JakePeak/BLE-Motion-Tracker/Windows_Application/BLE_Computer_Interaction/BLE_Computer_Interaction/resource.h

//{{NO_DEPENDENCIES}}
// Microsoft Visual C++ generated include file.
// Used by BLE_Computer_Interaction.rc
//
#define IDC_MYICON                      2
#define IDD_BLECOMPUTERINTERACTION_DIALOG 102
#define IDS_APP_TITLE                   103
#define IDD_ABOUTBOX                    103
#define IDM_ABOUT                       104
#define IDM_EXIT                        105
#define IDI_BLECOMPUTERINTERACTION      107
#define IDI_SMALL                       108
#define IDC_BLECOMPUTERINTERACTION      109
#define IDR_MAINFRAME                   128
#define IDD_ERRORBOX                    129
#define MAINICON                        1
#define IDC_STATIC                      -1

// Next default values for new objects
// 
#ifdef APSTUDIO_INVOKED
#ifndef APSTUDIO_READONLY_SYMBOLS
#define _APS_NO_MFC                     1
#define _APS_NEXT_RESOURCE_VALUE        131
#define _APS_NEXT_COMMAND_VALUE         32771
#define _APS_NEXT_CONTROL_VALUE         1000
#define _APS_NEXT_SYMED_VALUE           110
#endif
#endif
