JakePeak/BLE-Motion-Tracker/Firmware/Altered_Source_Files/SensorDemo_config.h

#define _SENSORDEMO_CONFIG_H_
#include "bluenrg1_stack.h"
#include "stack_user_cfg.h"
#include "OTA_btl.h"
#define MIN_NUM_LINK            1
#define DEFAULT_NUM_GATT_SERVICES   2
#define DEFAULT_NUM_GATT_ATTRIBUTES 9
#if (CONTROLLER_DATA_LENGTH_EXTENSION_ENABLED == 1) && (OTA_EXTENDED_PACKET_LEN == 1)
  #define OTA_MAX_ATT_MTU_SIZE    (OTA_ATT_MTU_SIZE) //(220) /* OTA Client & Server supported ATT_MTU */
#else
  #define OTA_MAX_ATT_MTU_SIZE    (DEFAULT_ATT_MTU)
#endif
#if defined (ST_OTA_LOWER_APPLICATION) || defined (ST_OTA_HIGHER_APPLICATION)
#define NUM_APP_GATT_SERVICES (2 + 1)
#ifdef SENSOR_EMULATION
#define NUM_APP_GATT_ATTRIBUTES (15 + 9)
#else  // No Humidity char
#define NUM_APP_GATT_ATTRIBUTES (12 + 9)
#endif
#define OTA_16_BYTES_BLOCKS_NUMBER ((OTA_MAX_ATT_MTU_SIZE-4)/16)
#define OTA_MAX_ATT_SIZE (4 + OTA_16_BYTES_BLOCKS_NUMBER * 16)
#else
#define NUM_APP_GATT_SERVICES 5
#ifdef SENSOR_EMULATION
#define NUM_APP_GATT_ATTRIBUTES 42//(34) /* 15 attributes x BLE Sensor demo services characteristics */
#else  // No Humidity char
#define NUM_APP_GATT_ATTRIBUTES (12)
#endif
#define OTA_MAX_ATT_SIZE (0)
#endif
#define MAX_CHAR_LEN(a,b) ((a) > (b) )? (a) : (b)
#define _MAX_ATT_SIZE	(120)
#define APP_MAX_ATT_SIZE	  MAX_CHAR_LEN(OTA_MAX_ATT_SIZE,  _MAX_ATT_SIZE)
#define NUM_LINKS               (MIN_NUM_LINK)
#define MAX_NUMBER_ATTRIBUTES_RECORDS_SERVICE_1 (6)
#ifdef SENSOR_EMULATION
#define MAX_NUMBER_ATTRIBUTES_RECORDS_SERVICE_2 (25)
#else
#define MAX_NUMBER_ATTRIBUTES_RECORDS_SERVICE_2 (7)
#endif
#define NUM_GATT_ATTRIBUTES     (DEFAULT_NUM_GATT_ATTRIBUTES + NUM_APP_GATT_ATTRIBUTES)
#define NUM_GATT_SERVICES       (DEFAULT_NUM_GATT_SERVICES + NUM_APP_GATT_SERVICES)
#if defined (ST_OTA_LOWER_APPLICATION) || defined (ST_OTA_HIGHER_APPLICATION)
#define OTA_ATT_VALUE_ARRAY_SIZE (99 + (4 + (OTA_16_BYTES_BLOCKS_NUMBER * 16)))
#else
#define OTA_ATT_VALUE_ARRAY_SIZE (0)
#endif
#ifdef SENSOR_EMULATION
#define ATT_VALUE_ARRAY_SIZE    (450 + OTA_ATT_VALUE_ARRAY_SIZE)//(43 + 106 + 28 + OTA_ATT_VALUE_ARRAY_SIZE) //(GATT + GAP) = 43 (Device Name: BlueNRG) + Acceleration (Acceleration (27) + Free Fall (21) characteristics) +  Environmental Sensor (Temperature (28) , Pressure (29), Humidity (28) characteristics)  Services
#else
#define ATT_VALUE_ARRAY_SIZE    (43 + 106  + OTA_ATT_VALUE_ARRAY_SIZE) //(GATT + GAP) = 43 (Device Name: BlueNRG) + Acceleration (Acceleration (27) + Free Fall (21) characteristics) +  Environmental Sensor (Temperature (28), Pressure (29)  characteristics)  Services
#endif
#define FLASH_SEC_DB_SIZE       (0x400)
#define FLASH_SERVER_DB_SIZE    (0x400)
#if (CONTROLLER_DATA_LENGTH_EXTENSION_ENABLED == 1) && (OTA_EXTENDED_PACKET_LEN == 1)
  #define MAX_ATT_MTU             (OTA_MAX_ATT_MTU_SIZE)
#else
  #define MAX_ATT_MTU             (DEFAULT_ATT_MTU)
#endif
#define MAX_ATT_SIZE            (APP_MAX_ATT_SIZE)
#define PREPARE_WRITE_LIST_SIZE PREP_WRITE_X_ATT(MAX_ATT_SIZE)
#define OPT_MBLOCKS		(6)
#define MBLOCKS_COUNT           (MBLOCKS_CALC(PREPARE_WRITE_LIST_SIZE, MAX_ATT_MTU, NUM_LINKS) + OPT_MBLOCKS)
NO_INIT(uint32_t dyn_alloc_a[TOTAL_BUFFER_SIZE(NUM_LINKS,NUM_GATT_ATTRIBUTES,NUM_GATT_SERVICES,ATT_VALUE_ARRAY_SIZE,MBLOCKS_COUNT,CONTROLLER_DATA_LENGTH_EXTENSION_ENABLED)>>2]);
NO_INIT_SECTION(uint32_t stacklib_flash_data[TOTAL_FLASH_BUFFER_SIZE(FLASH_SEC_DB_SIZE, FLASH_SERVER_DB_SIZE)>>2], ".noinit.stacklib_flash_data");
NO_INIT_SECTION(uint8_t stacklib_stored_device_id_data[56], ".noinit.stacklib_stored_device_id_data");
#define MAX_CONN_EVENT_LENGTH 0xFFFFFFFF
#if (LS_SOURCE == LS_SOURCE_INTERNAL_RO)
#define SLAVE_SLEEP_CLOCK_ACCURACY 500
#define MASTER_SLEEP_CLOCK_ACCURACY MASTER_SCA_500ppm
#else
#define SLAVE_SLEEP_CLOCK_ACCURACY 100
#define MASTER_SLEEP_CLOCK_ACCURACY MASTER_SCA_100ppm
#endif
#if (LS_SOURCE == LS_SOURCE_INTERNAL_RO)
#define LOW_SPEED_SOURCE  1 // Internal RO
#else
#define LOW_SPEED_SOURCE  0 // External 32 KHz
#endif
#define HS_STARTUP_TIME 328 // 800 us
extern uint8_t hot_table_radio_config[];
#define CONFIG_TABLE            \
{                               \
  (uint32_t*)hot_table_radio_config,          \
  MAX_CONN_EVENT_LENGTH,        \
  SLAVE_SLEEP_CLOCK_ACCURACY,   \
  MASTER_SLEEP_CLOCK_ACCURACY,  \
  LOW_SPEED_SOURCE,             \
  HS_STARTUP_TIME               \
}
const BlueNRG_Stack_Initialization_t BlueNRG_Stack_Init_params = {
    (uint8_t*)stacklib_flash_data,
    FLASH_SEC_DB_SIZE,
    FLASH_SERVER_DB_SIZE,
    (uint8_t*)stacklib_stored_device_id_data,
    (uint8_t*)dyn_alloc_a,
    TOTAL_BUFFER_SIZE(NUM_LINKS,NUM_GATT_ATTRIBUTES,NUM_GATT_SERVICES,ATT_VALUE_ARRAY_SIZE,MBLOCKS_COUNT,CONTROLLER_DATA_LENGTH_EXTENSION_ENABLED),
    NUM_GATT_ATTRIBUTES,
    NUM_GATT_SERVICES,
    ATT_VALUE_ARRAY_SIZE,
    NUM_LINKS,
    0,
    PREPARE_WRITE_LIST_SIZE,
    MBLOCKS_COUNT,
    MAX_ATT_MTU,
    CONFIG_TABLE,
};
